AlexandreLuce/PPA1200MegaControl/Docs/Datasheets/2sa1494-pinout.jpg

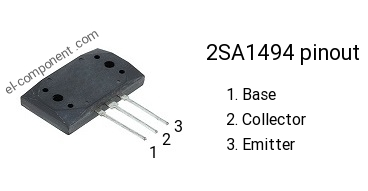
Docs/Datasheets/2sa1494-pinout.jpg
