AlexandreLuce/PPA1200MegaControl/Arduino/STAGE_Control/VolumeTable.h

/*******************************************************
*
*
* Volume table for control volume fonction
* 
* 
*******************************************************/

const byte ADVol[81][12] = {     
                          {0,0,0,0,0,0,0,0,0,0,0,0}, //0
                          {0,0,0,0,0,0,0,1,0,1,0,0}, //20
					                {0,0,0,0,0,0,1,0,1,0,0,1}, //41
                          {0,0,0,0,0,0,1,1,1,1,0,1}, //61
                          {0,0,0,0,0,1,0,1,0,0,1,0}, //82
                          {0,0,0,0,0,1,1,0,0,1,1,1}, //103
					                {0,0,0,0,0,1,1,1,1,0,1,1}, //123
                          {0,0,0,0,1,0,0,1,0,0,0,1}, //145
                          {0,0,0,0,1,0,1,0,0,1,0,0}, //164
                          {0,0,0,0,1,0,1,1,1,0,1,0}, //186
						              {0,0,0,0,1,1,0,0,1,1,0,1}, //205
                          {0,0,0,0,1,1,1,0,0,0,1,1}, //227
                          {0,0,0,0,1,1,1,1,0,1,1,0}, //246
                          {0,0,0,1,0,0,0,0,1,1,0,0}, //268
					                {0,0,0,1,0,0,0,1,1,1,1,1}, //287
                          {0,0,0,1,0,0,1,1,0,1,0,1}, //309
                          {0,0,0,1,0,1,0,0,1,0,0,0}, //328
                          {0,0,0,1,0,1,0,1,1,1,0,1}, //349
						              {0,0,0,1,0,1,1,1,0,0,0,1}, //369
                          {0,0,0,1,1,0,0,0,0,1,1,0}, //390
                          {0,0,0,1,1,0,0,1,1,0,1,0}, //410
						              {0,0,0,1,1,1,0,0,0,0,1,1}, //451
                          {0,0,0,1,1,1,1,0,1,0,1,1}, //491
						              {0,0,1,0,0,0,0,1,0,1,0,0}, //532
                          {0,0,1,0,0,0,1,1,1,1,0,1}, //573
					            	  {0,0,1,0,0,1,1,0,0,1,1,0}, //614
                          {0,0,1,0,1,0,0,0,1,1,1,1}, //655
				            		  {0,0,1,0,1,0,1,1,1,0,0,0}, //696
                          {0,0,1,0,1,1,1,0,0,0,0,1}, //737
				             		  {0,0,1,1,0,0,0,0,1,0,1,0}, //778
                          {0,0,1,1,0,0,1,1,0,0,1,1}, //819
					             	  {0,0,1,1,0,1,0,1,1,1,0,0}, //860
                          {0,0,1,1,1,0,0,0,0,1,0,1}, //901
						              {0,0,1,1,1,0,1,0,1,1,1,0}, //942
                          {0,0,1,1,1,1,0,1,0,1,1,1}, //983
						              {0,1,0,0,0,0,0,0,0,0,0,0}, //1024
                          {0,1,0,0,0,0,1,0,1,0,0,1}, //1065
						              {0,1,0,0,0,1,0,1,0,0,1,0}, //1106
                          {0,1,0,0,0,1,1,1,1,0,1,1}, //1147
						              {0,1,0,0,1,0,1,0,0,1,0,0}, //1188
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
                          };

/*******************************************************
* End of File 
*******************************************************/

/*******************************************************
*
*
* Replace Table fonction
* 
* 
*******************************************************/

void replaceVolTable()
{
int myNum = 50;
int zeros = String(myNum,BIN).length();//This will check for the length of myNum in binary.
Serial.println(zeros); //For myNum = 50. You will get a 6.
delay(1000);

String myStr;
for (int i=0; i < 16 - zeros; i++) {//This will add zero to string as need
myStr = myStr + "0";
}
myStr = myStr + String(myNum,BIN);//Gives 0000000000110010
Serial.println(myStr);
delay(1000);
}
